gctechspace/vendingMachine/NextionDisplay/keypad.jpg

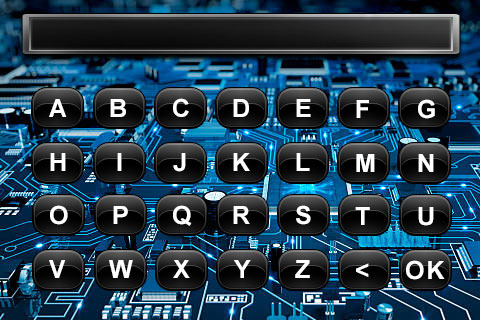
NextionDisplay/keypad.jpg
