gctechspace/vendingMachine/NextionDisplay/keypadP.jpg

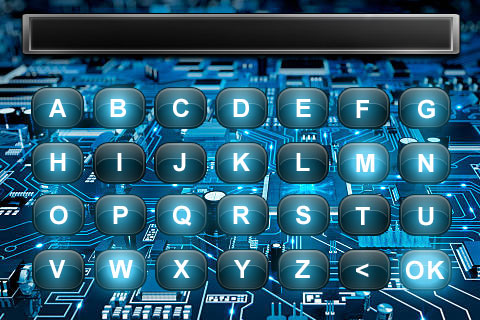
NextionDisplay/keypadP.jpg
