gctechspace/vendingMachine/NextionDisplay/letters.jpg

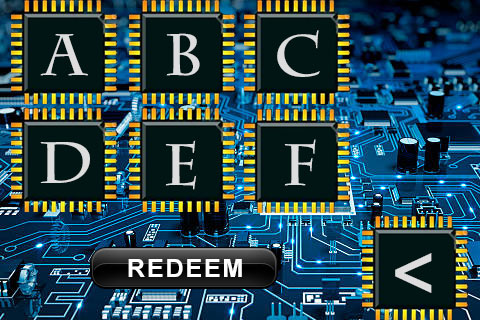
NextionDisplay/letters.jpg
