gctechspace/vendingMachine/NextionDisplay/lettersP.jpg

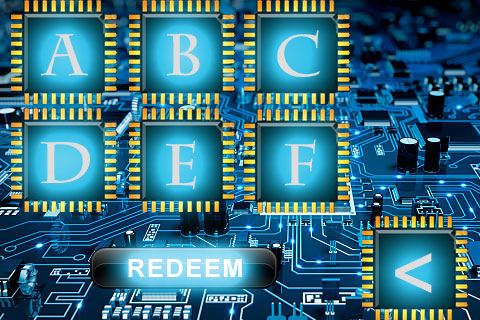
NextionDisplay/lettersP.jpg
