gctechspace/vendingMachine/NextionDisplay/money.jpg

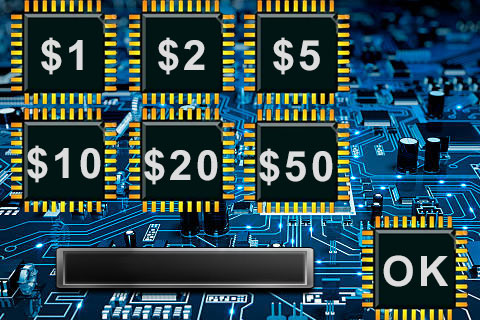
NextionDisplay/money.jpg
