gctechspace/vendingMachine/NextionDisplay/moneyP.jpg

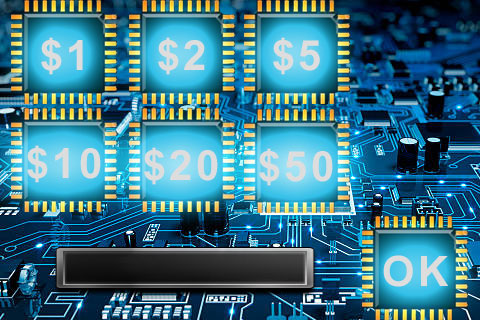
NextionDisplay/moneyP.jpg
