gctechspace/vendingMachine/NextionDisplay/numbers5.jpg

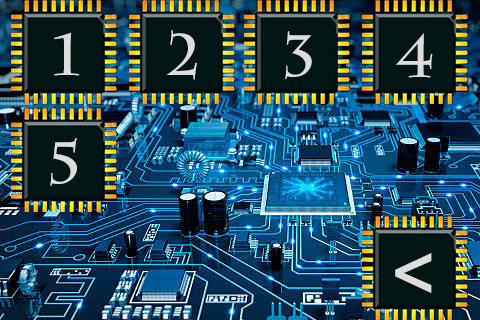
NextionDisplay/numbers5.jpg
