gctechspace/vendingMachine/NextionDisplay/numbers.jpg

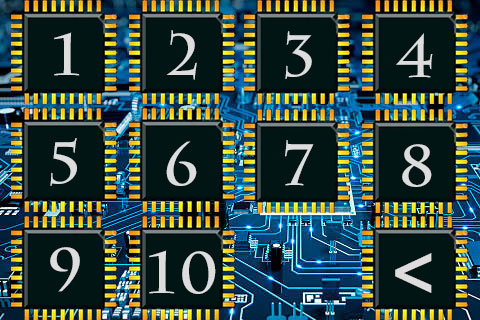
NextionDisplay/numbers.jpg
