gctechspace/vendingMachine/NextionDisplay/numbersP.jpg

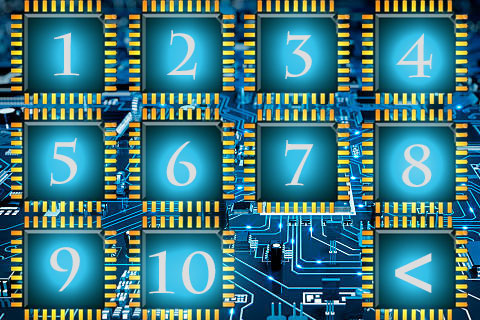
NextionDisplay/numbersP.jpg
