gctechspace/vendingMachine/NextionDisplay/OfO.jpg

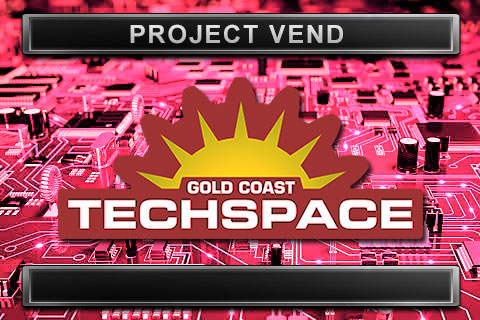
NextionDisplay/OfO.jpg
