gctechspace/vendingMachine/PCB/PCB-CONNECTORS.png

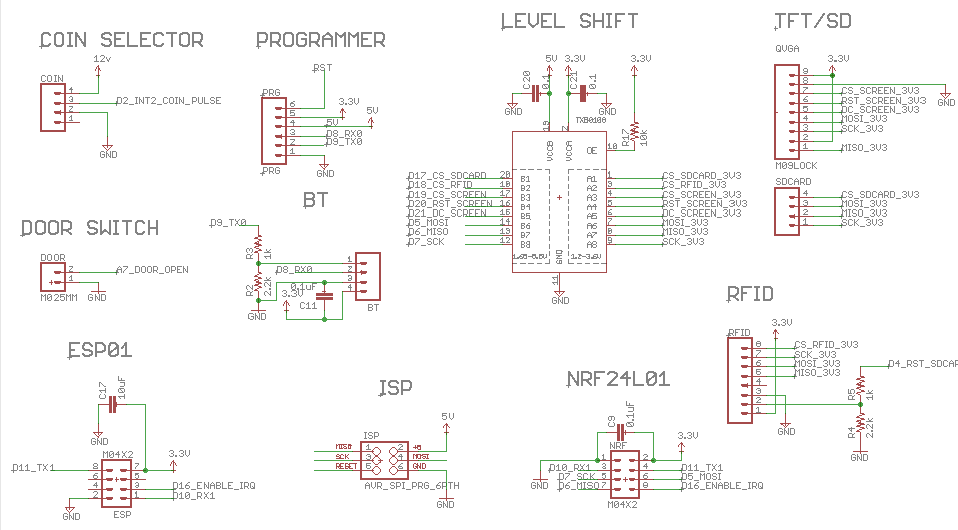
PCB/PCB-CONNECTORS.png
