gctechspace/vendingMachine/PCB/PCB-Despence.png

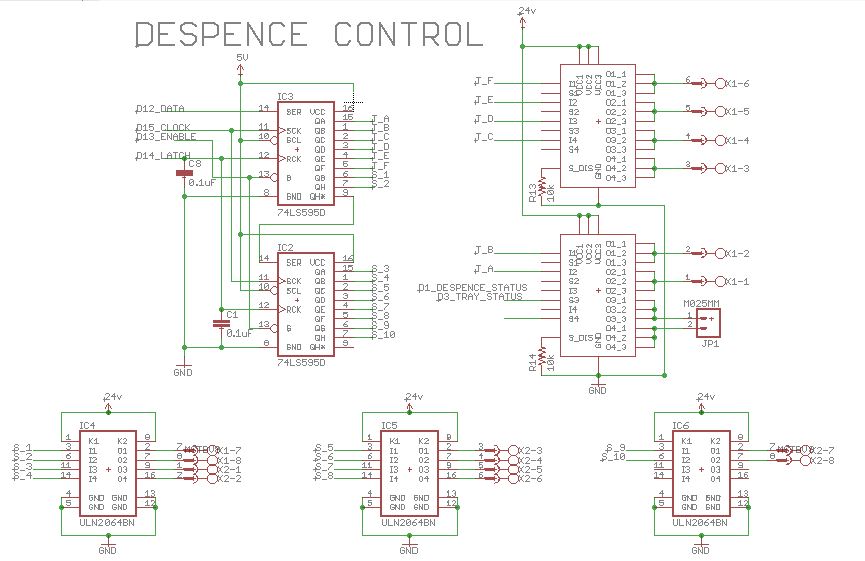
PCB/PCB-Despence.png
