gctechspace/vendingMachine/Arduino/vending-atmega/rfid.ino

void rfidInit(){
  mfrc522.PCD_Init();        // Init MFRC522 card
}

void detectTag(){
  // Prepare key - all keys are set to FFFFFFFFFFFFh at chip delivery from the factory.
  MFRC522::MIFARE_Key key;
  for (byte i = 0; i < 6; i++) key.keyByte[i] = 0xFF;

  // Look for new cards
  if ( ! mfrc522.PICC_IsNewCardPresent()) {
    return;
  }

  // Select one of the cards
  if ( ! mfrc522.PICC_ReadCardSerial())    return;

  String packet_str;
  Serial.print("Card UID:");    //Dump UID
  for (byte i = 0; i < mfrc522.uid.size; i++) {
    Serial.print(mfrc522.uid.uidByte[i] < 0x10 ? " 0" : " ");
    Serial.print(mfrc522.uid.uidByte[i], HEX);
    packet_str += mfrc522.uid.uidByte[i];
  } 
  Serial.println();
  Serial.println(packet_str);
  Serial.println();
}
